Allan-Nava/keycaps/asus-rog-falchion-ace/left-shift-preview-top.png

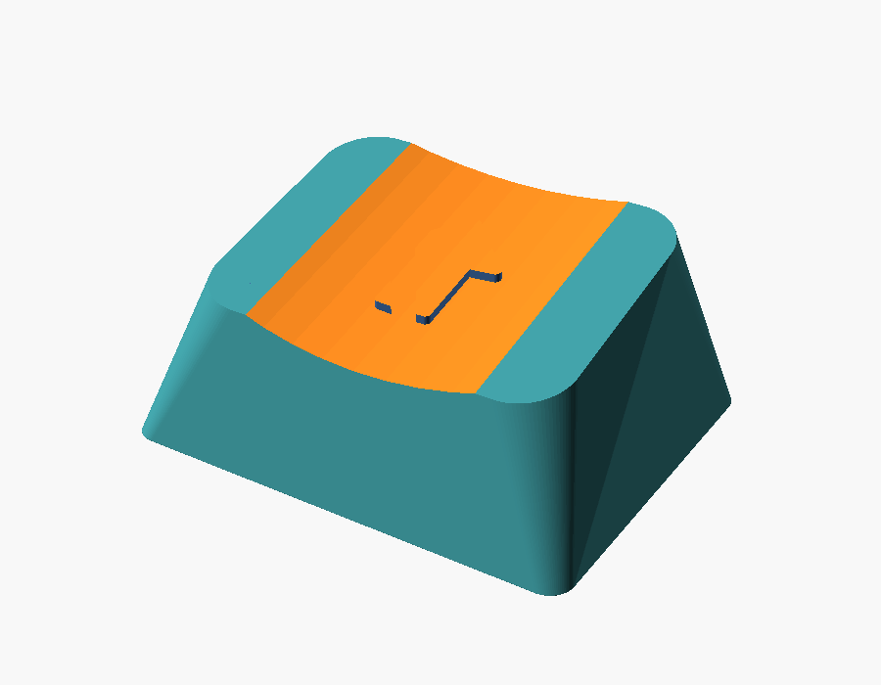
asus-rog-falchion-ace/left-shift-preview-top.png
