Allan-Nava/keycaps/ozone-strike-battle/left-shift-ansi-drawing.png

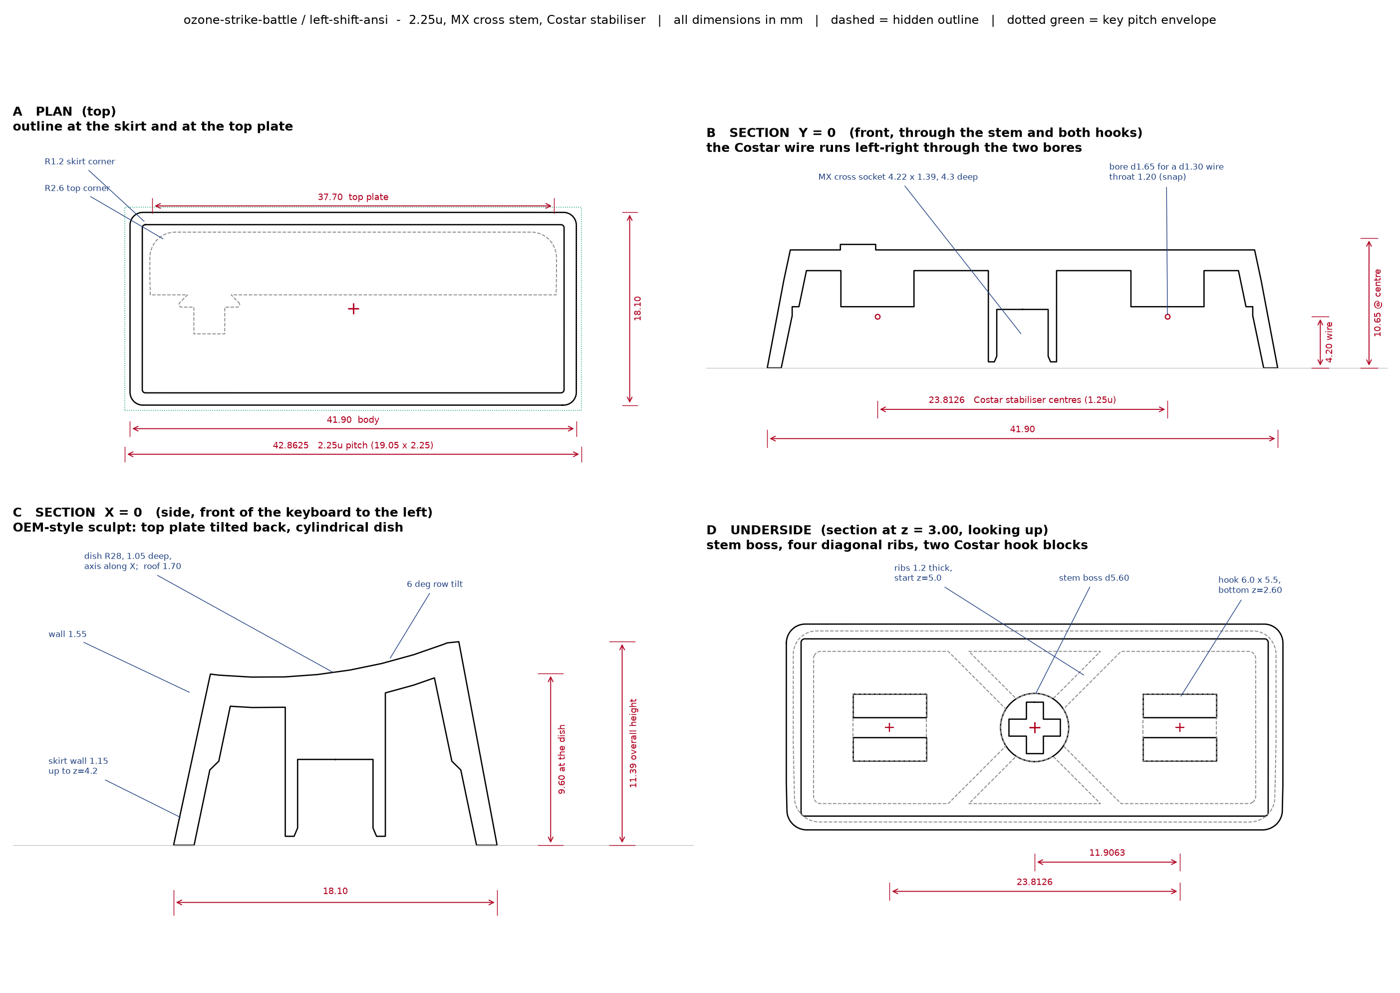
ozone-strike-battle/left-shift-ansi-drawing.png
