Allan-Nava/keycaps/ozone-strike-battle/left-shift-ansi-preview-top.png

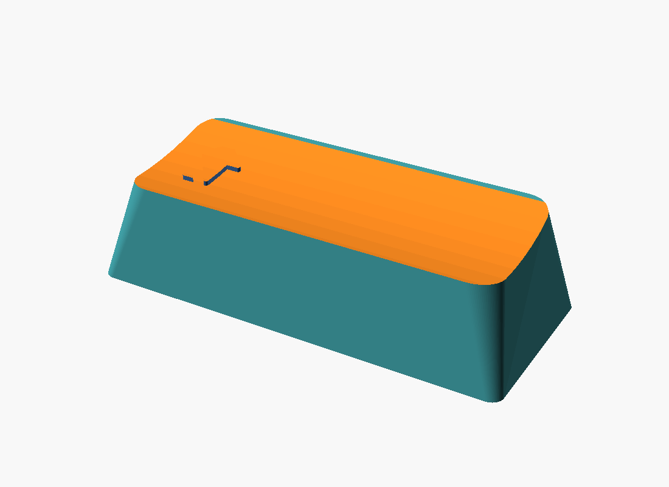
ozone-strike-battle/left-shift-ansi-preview-top.png
