Allan-Nava/keycaps/ozone-strike-battle/left-shift-ansi-preview-underside.png

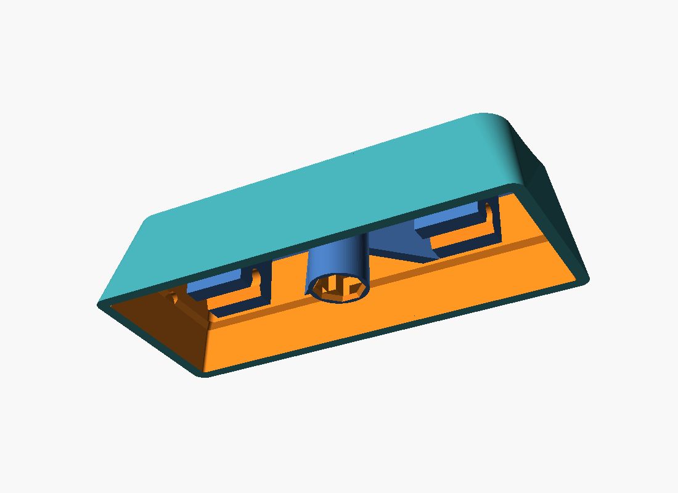
ozone-strike-battle/left-shift-ansi-preview-underside.png
